jfedor2/hid-remapper/custom-boards/v6/3d-printed-case/Remapper-v6-Top-with-labels.stl

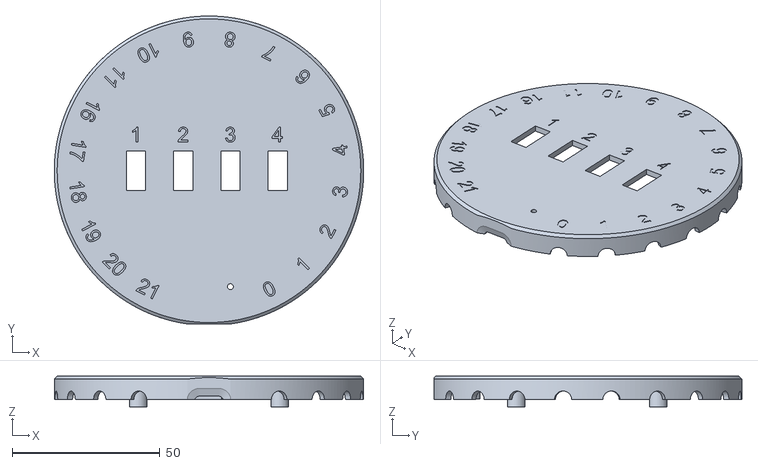
[picture p27: CAD file, 2024-04-09, an earlier design]
custom-boards/v6/3d-printed-case/Remapper-v6-Top-with-labels.stl
104.8 x 104.3 x 10.4
