jfedor2/hid-remapper/custom-boards/v7/3d-printed-case/Remapper-v7-Top-with-labels.stl

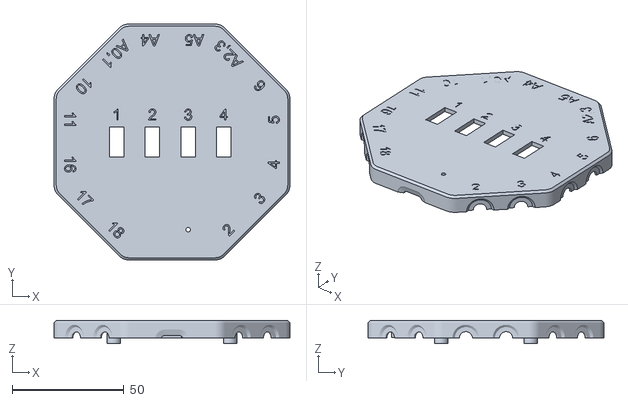
[picture p28: CAD file, 2024-04-09, an earlier design]
custom-boards/v7/3d-printed-case/Remapper-v7-Top-with-labels.stl
105.6 x 105.6 x 10.4
