jfedor2/hid-remapper/custom-boards/v1/3d-printed-case/Remapper-v1-Bottom.stl

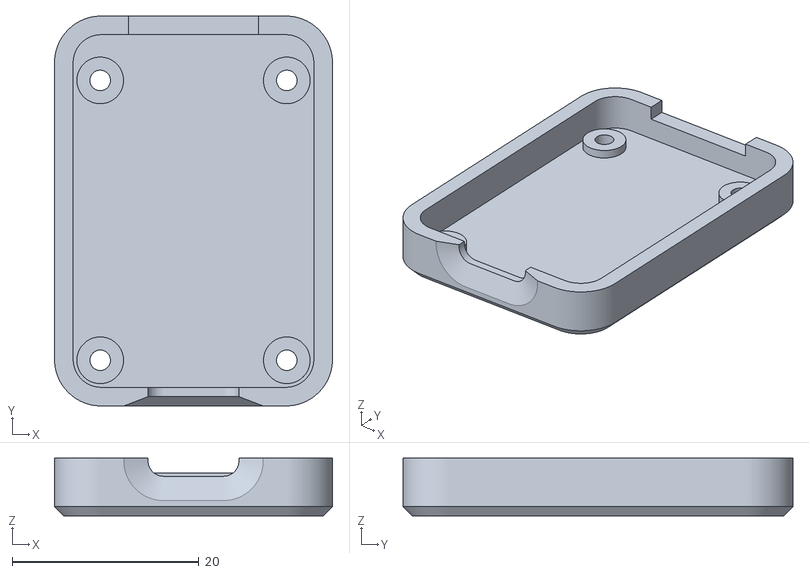
[picture p29: CAD file, 2022-11-09, an earlier design]
custom-boards/v1/3d-printed-case/Remapper-v1-Bottom.stl
29.8 x 41.8 x 6.20
