jfedor2/hid-remapper/firmware/src/boards/waveshare_rp2350_pizero.h

// -----------------------------------------------------
// NOTE: THIS HEADER IS ALSO INCLUDED BY ASSEMBLER SO
//       SHOULD ONLY CONSIST OF PREPROCESSOR DIRECTIVES
// -----------------------------------------------------

// pico_cmake_set PICO_PLATFORM=rp2350

#ifndef _BOARDS_WAVESHARE_RP2350_PIZERO_H
#define _BOARDS_WAVESHARE_RP2350_PIZERO_H

#define WAVESHARE_RP2350_PIZERO_BOARD

#define PICO_RP2350B 1

#define GPIO_VALID_PINS_BASE 0b00111111111111111111111111111111

#define PICO_DEFAULT_PIO_USB_DP_PIN 28

// --- FLASH ---

#define PICO_BOOT_STAGE2_CHOOSE_W25Q080 1

#ifndef PICO_FLASH_SPI_CLKDIV
#define PICO_FLASH_SPI_CLKDIV 2
#endif

#ifndef PICO_FLASH_SIZE_BYTES
#define PICO_FLASH_SIZE_BYTES (16 * 1024 * 1024)
#endif

#ifndef PICO_RP2350_A2_SUPPORTED
#define PICO_RP2350_A2_SUPPORTED 1
#endif

#endif
