jfedor2/hid-remapper/firmware/src/globals.cc

#include "globals.h"

std::unordered_map<uint16_t, std::unordered_map<uint8_t, std::unordered_map<uint32_t, usage_def_t>>> their_usages;
std::unordered_map<uint16_t, std::unordered_map<uint8_t, std::unordered_map<uint32_t, usage_def_t>>> their_out_usages;
std::unordered_map<uint16_t, std::unordered_map<uint8_t, std::unordered_map<uint32_t, usage_def_t>>> their_feature_usages;

std::unordered_map<uint16_t, bool> has_report_id_theirs;

std::unordered_map<uint32_t, uint8_t*> out_reports;
std::unordered_map<uint32_t, uint8_t*> prev_out_reports;
std::unordered_map<uint32_t, uint8_t> out_report_sizes;
std::unordered_map<uint32_t, std::vector<uint32_t>> their_out_usages_flat;

std::unordered_map<uint16_t, uint8_t> interface_index;
uint32_t interface_index_in_use = 0;

std::vector<usage_rle_t> our_usages_rle;
std::vector<usage_rle_t> their_usages_rle;

volatile bool need_to_persist_config = false;
volatile bool their_descriptor_updated = false;
volatile bool suspended = false;
volatile bool resume_pending = false;
volatile bool config_updated = false;

uint8_t unmapped_passthrough_layer_mask = 0b11111111;
uint32_t partial_scroll_timeout = 1000000;
uint32_t tap_hold_threshold = 200000;
uint64_t gpio_debounce_time = 5000;
uint8_t our_descriptor_number = 0;
bool ignore_auth_dev_inputs = false;
uint8_t macro_entry_duration = 0;  // 0 means 1ms
uint8_t gpio_output_mode = 0;
bool normalize_gamepad_inputs = true;

std::vector<mapping_config11_t> config_mappings;

uint8_t resolution_multiplier = 0;

std::vector<std::vector<uint32_t>> macros[NMACROS];

std::vector<expr_elem_t> expressions[NEXPRESSIONS];

bool monitor_enabled = false;

const our_descriptor_def_t* our_descriptor;

uint8_t gpio_out_state[4] = { 0 };
uint16_t digipot_state[NDIGIPOTS] = { 0 };

std::vector<quirk_t> quirks;

bool boot_protocol_keyboard = false;
bool boot_protocol_updated = false;

volatile PersistConfigReturnCode persist_config_return_code = PersistConfigReturnCode::UNKNOWN;
