jfedor2/hid-remapper/config-tool-web/usages.js

const usages = {
    'source_0': {
        "0x00090001": { 'name': 'Left button', 'class': 'mouse' },
        "0x00090002": { 'name': 'Right button', 'class': 'mouse' },
        "0x00090003": { 'name': 'Middle button', 'class': 'mouse' },
        "0x00090004": { 'name': 'Back', 'class': 'mouse' },
        "0x00090005": { 'name': 'Forward', 'class': 'mouse' },
        "0x00090006": { 'name': 'Button 6', 'class': 'mouse' },
        "0x00090007": { 'name': 'Button 7', 'class': 'mouse' },
        "0x00090008": { 'name': 'Button 8', 'class': 'mouse' },
        "0x00010030": { 'name': 'Cursor X', 'class': 'mouse' },
        "0x00010031": { 'name': 'Cursor Y', 'class': 'mouse' },
        "0x00010038": { 'name': 'V scroll', 'class': 'mouse' },
        "0x000c0238": { 'name': 'H scroll', 'class': 'mouse' },
    },
    'source_1': {
        "0x00010030": { 'name': 'Left stick X', 'class': 'gamepad' },
        "0x00010031": { 'name': 'Left stick Y', 'class': 'gamepad' },
        "0x00010032": { 'name': 'Right stick X', 'class': 'gamepad' },
        "0x00010035": { 'name': 'Right stick Y', 'class': 'gamepad' },
        "0xfff90001": { 'name': 'D-pad left', 'class': 'gamepad' },
        "0xfff90002": { 'name': 'D-pad right', 'class': 'gamepad' },
        "0xfff90003": { 'name': 'D-pad up', 'class': 'gamepad' },
        "0xfff90004": { 'name': 'D-pad down', 'class': 'gamepad' },
        "0x00090001": { 'name': 'West', 'class': 'gamepad' },
        "0x00090002": { 'name': 'South', 'class': 'gamepad' },
        "0x00090003": { 'name': 'East', 'class': 'gamepad' },
        "0x00090004": { 'name': 'North', 'class': 'gamepad' },
        "0x00090005": { 'name': 'L1', 'class': 'gamepad' },
        "0x00090006": { 'name': 'R1', 'class': 'gamepad' },
        "0x00090007": { 'name': 'L2', 'class': 'gamepad' },
        "0x00090008": { 'name': 'R2', 'class': 'gamepad' },
        "0x00010033": { 'name': 'L2 axis', 'class': 'gamepad' },
        "0x00010034": { 'name': 'R2 axis', 'class': 'gamepad' },
        "0x00090009": { 'name': 'Select', 'class': 'gamepad' },
        "0x0009000a": { 'name': 'Start', 'class': 'gamepad' },
        "0x0009000b": { 'name': 'L3', 'class': 'gamepad' },
        "0x0009000c": { 'name': 'R3', 'class': 'gamepad' },
        "0x0009000d": { 'name': 'Home', 'class': 'gamepad' },
        "0x0009000e": { 'name': 'Button 14', 'class': 'gamepad' },
        "0x0009000f": { 'name': 'Button 15', 'class': 'gamepad' },
        "0x00090010": { 'name': 'Button 16', 'class': 'gamepad' },
    },
    'source_extra': {
        "0x00010038": { 'name': 'V scroll', 'class': 'mouse' },
        "0x000c0238": { 'name': 'H scroll', 'class': 'mouse' },
        "0x00010032": { 'name': 'Right stick X', 'class': 'gamepad' },
        "0x00010035": { 'name': 'Right stick Y', 'class': 'gamepad' },
        "0xfff90001": { 'name': 'D-pad left', 'class': 'gamepad' },
        "0xfff90002": { 'name': 'D-pad right', 'class': 'gamepad' },
        "0xfff90003": { 'name': 'D-pad up', 'class': 'gamepad' },
        "0xfff90004": { 'name': 'D-pad down', 'class': 'gamepad' },
        "0x00010033": { 'name': 'L2 axis', 'class': 'gamepad' },
        "0x00010034": { 'name': 'R2 axis', 'class': 'gamepad' },
        "0x000200c5": { 'name': 'Brake', 'class': 'mouse' },
        "0x000200c4": { 'name': 'Accelerator', 'class': 'mouse' },
    },
    'source': {
        "0x000700e0": { 'name': 'Left Control', 'class': 'keyboard' },
        "0x000700e1": { 'name': 'Left Shift', 'class': 'keyboard' },
        "0x000700e2": { 'name': 'Left Alt', 'class': 'keyboard' },
        "0x000700e3": { 'name': 'Left GUI', 'class': 'keyboard' },
        "0x000700e4": { 'name': 'Right Control', 'class': 'keyboard' },
        "0x000700e5": { 'name': 'Right Shift', 'class': 'keyboard' },
        "0x000700e6": { 'name': 'Right Alt', 'class': 'keyboard' },
        "0x000700e7": { 'name': 'Right GUI', 'class': 'keyboard' },
        "0x00070004": { 'name': 'A', 'class': 'keyboard' },
        "0x00070005": { 'name': 'B', 'class': 'keyboard' },
        "0x00070006": { 'name': 'C', 'class': 'keyboard' },
        "0x00070007": { 'name': 'D', 'class': 'keyboard' },
        "0x00070008": { 'name': 'E', 'class': 'keyboard' },
        "0x00070009": { 'name': 'F', 'class': 'keyboard' },
        "0x0007000a": { 'name': 'G', 'class': 'keyboard' },
        "0x0007000b": { 'name': 'H', 'class': 'keyboard' },
        "0x0007000c": { 'name': 'I', 'class': 'keyboard' },
        "0x0007000d": { 'name': 'J', 'class': 'keyboard' },
        "0x0007000e": { 'name': 'K', 'class': 'keyboard' },
        "0x0007000f": { 'name': 'L', 'class': 'keyboard' },
        "0x00070010": { 'name': 'M', 'class': 'keyboard' },
        "0x00070011": { 'name': 'N', 'class': 'keyboard' },
        "0x00070012": { 'name': 'O', 'class': 'keyboard' },
        "0x00070013": { 'name': 'P', 'class': 'keyboard' },
        "0x00070014": { 'name': 'Q', 'class': 'keyboard' },
        "0x00070015": { 'name': 'R', 'class': 'keyboard' },
        "0x00070016": { 'name': 'S', 'class': 'keyboard' },
        "0x00070017": { 'name': 'T', 'class': 'keyboard' },
        "0x00070018": { 'name': 'U', 'class': 'keyboard' },
        "0x00070019": { 'name': 'V', 'class': 'keyboard' },
        "0x0007001a": { 'name': 'W', 'class': 'keyboard' },
        "0x0007001b": { 'name': 'X', 'class': 'keyboard' },
        "0x0007001c": { 'name': 'Y', 'class': 'keyboard' },
        "0x0007001d": { 'name': 'Z', 'class': 'keyboard' },
        "0x0007001e": { 'name': '1', 'class': 'keyboard' },
        "0x0007001f": { 'name': '2', 'class': 'keyboard' },
        "0x00070020": { 'name': '3', 'class': 'keyboard' },
        "0x00070021": { 'name': '4', 'class': 'keyboard' },
        "0x00070022": { 'name': '5', 'class': 'keyboard' },
        "0x00070023": { 'name': '6', 'class': 'keyboard' },
        "0x00070024": { 'name': '7', 'class': 'keyboard' },
        "0x00070025": { 'name': '8', 'class': 'keyboard' },
        "0x00070026": { 'name': '9', 'class': 'keyboard' },
        "0x00070027": { 'name': '0', 'class': 'keyboard' },
        "0x00070028": { 'name': 'Enter', 'class': 'keyboard' },
        "0x00070029": { 'name': 'Escape', 'class': 'keyboard' },
        "0x0007002a": { 'name': 'Backspace', 'class': 'keyboard' },
        "0x0007002b": { 'name': 'Tab', 'class': 'keyboard' },
        "0x0007002c": { 'name': 'Space', 'class': 'keyboard' },
        "0x00070039": { 'name': 'Caps Lock', 'class': 'keyboard' },
        "0x00070046": { 'name': 'PrintScreen', 'class': 'keyboard' },
        "0x00070047": { 'name': 'Scroll Lock', 'class': 'keyboard' },
        "0x00070048": { 'name': 'Pause', 'class': 'keyboard' },
        "0x00070049": { 'name': 'Insert', 'class': 'keyboard' },
        "0x0007004a": { 'name': 'Home', 'class': 'keyboard' },
        "0x0007004b": { 'name': 'PageUp', 'class': 'keyboard' },
        "0x0007004c": { 'name': 'Delete', 'class': 'keyboard' },
        "0x0007004d": { 'name': 'End', 'class': 'keyboard' },
        "0x0007004e": { 'name': 'PageDown', 'class': 'keyboard' },
        "0x0007004f": { 'name': 'Right arrow', 'class': 'keyboard' },
        "0x00070050": { 'name': 'Left arrow', 'class': 'keyboard' },
        "0x00070051": { 'name': 'Down arrow', 'class': 'keyboard' },
        "0x00070052": { 'name': 'Up arrow', 'class': 'keyboard' },
        "0x00070053": { 'name': 'Num Lock', 'class': 'keyboard' },
        "0x0007002d": { 'name': '- _', 'class': 'keyboard' },
        "0x0007002e": { 'name': '= +', 'class': 'keyboard' },
        "0x0007002f": { 'name': '[ {', 'class': 'keyboard' },
        "0x00070030": { 'name': '] }', 'class': 'keyboard' },
        "0x00070031": { 'name': '\\ |', 'class': 'keyboard' },
        "0x00070033": { 'name': '; :', 'class': 'keyboard' },
        "0x00070034": { 'name': '‘ “', 'class': 'keyboard' },
        "0x00070035": { 'name': '` ~', 'class': 'keyboard' },
        "0x00070036": { 'name': ', <', 'class': 'keyboard' },
        "0x00070037": { 'name': '. >', 'class': 'keyboard' },
        "0x00070038": { 'name': '/ ?', 'class': 'keyboard' },
        "0x0007003a": { 'name': 'F1', 'class': 'keyboard' },
        "0x0007003b": { 'name': 'F2', 'class': 'keyboard' },
        "0x0007003c": { 'name': 'F3', 'class': 'keyboard' },
        "0x0007003d": { 'name': 'F4', 'class': 'keyboard' },
        "0x0007003e": { 'name': 'F5', 'class': 'keyboard' },
        "0x0007003f": { 'name': 'F6', 'class': 'keyboard' },
        "0x00070040": { 'name': 'F7', 'class': 'keyboard' },
        "0x00070041": { 'name': 'F8', 'class': 'keyboard' },
        "0x00070042": { 'name': 'F9', 'class': 'keyboard' },
        "0x00070043": { 'name': 'F10', 'class': 'keyboard' },
        "0x00070044": { 'name': 'F11', 'class': 'keyboard' },
        "0x00070045": { 'name': 'F12', 'class': 'keyboard' },
        "0x00070068": { 'name': 'F13', 'class': 'keyboard' },
        "0x00070069": { 'name': 'F14', 'class': 'keyboard' },
        "0x0007006a": { 'name': 'F15', 'class': 'keyboard' },
        "0x0007006b": { 'name': 'F16', 'class': 'keyboard' },
        "0x0007006c": { 'name': 'F17', 'class': 'keyboard' },
        "0x0007006d": { 'name': 'F18', 'class': 'keyboard' },
        "0x0007006e": { 'name': 'F19', 'class': 'keyboard' },
        "0x0007006f": { 'name': 'F20', 'class': 'keyboard' },
        "0x00070070": { 'name': 'F21', 'class': 'keyboard' },
        "0x00070071": { 'name': 'F22', 'class': 'keyboard' },
        "0x00070072": { 'name': 'F23', 'class': 'keyboard' },
        "0x00070073": { 'name': 'F24', 'class': 'keyboard' },
        "0x00070054": { 'name': 'Keypad /', 'class': 'keyboard' },
        "0x00070055": { 'name': 'Keypad *', 'class': 'keyboard' },
        "0x00070056": { 'name': 'Keypad -', 'class': 'keyboard' },
        "0x00070057": { 'name': 'Keypad +', 'class': 'keyboard' },
        "0x00070058": { 'name': 'Keypad Enter', 'class': 'keyboard' },
        "0x00070059": { 'name': 'Keypad 1', 'class': 'keyboard' },
        "0x0007005a": { 'name': 'Keypad 2', 'class': 'keyboard' },
        "0x0007005b": { 'name': 'Keypad 3', 'class': 'keyboard' },
        "0x0007005c": { 'name': 'Keypad 4', 'class': 'keyboard' },
        "0x0007005d": { 'name': 'Keypad 5', 'class': 'keyboard' },
        "0x0007005e": { 'name': 'Keypad 6', 'class': 'keyboard' },
        "0x0007005f": { 'name': 'Keypad 7', 'class': 'keyboard' },
        "0x00070060": { 'name': 'Keypad 8', 'class': 'keyboard' },
        "0x00070061": { 'name': 'Keypad 9', 'class': 'keyboard' },
        "0x00070062": { 'name': 'Keypad 0', 'class': 'keyboard' },
        "0x00070063": { 'name': 'Keypad .', 'class': 'keyboard' },
        "0x00070067": { 'name': 'Keypad =', 'class': 'keyboard' },
        "0x00070064": { 'name': 'Non-US \\ |', 'class': 'keyboard' },
        "0x00070032": { 'name': 'Non-US # ~', 'class': 'keyboard' },
        "0x00070065": { 'name': 'Application', 'class': 'keyboard' },
        "0x00070066": { 'name': 'Power', 'class': 'keyboard' },
        "0x00070087": { 'name': '\\ _', 'class': 'keyboard' },
        "0x00070089": { 'name': '¥ |', 'class': 'keyboard' },
        "0x0007008a": { 'name': 'Henkan', 'class': 'keyboard' },
        "0x0007008b": { 'name': 'Muhenkan', 'class': 'keyboard' },
        "0x00070088": { 'name': 'Kana', 'class': 'keyboard' },
        "0x00070090": { 'name': 'Kana (Mac)', 'class': 'keyboard' },
        "0x00070091": { 'name': 'Eisū (Mac)', 'class': 'keyboard' },
        "0x00080001": { 'name': 'Num Lock LED', 'class': 'keyboard' },
        "0x00080002": { 'name': 'Caps Lock LED', 'class': 'keyboard' },
        "0x00080003": { 'name': 'Scroll Lock LED', 'class': 'keyboard' },
        "0x00080004": { 'name': 'Compose LED', 'class': 'keyboard' },
        "0x00080005": { 'name': 'Kana LED', 'class': 'keyboard' },

        "0x000c00e9": { 'name': 'Volume up', 'class': 'media' },
        "0x000c00ea": { 'name': 'Volume down', 'class': 'media' },
        "0x000c00e2": { 'name': 'Mute', 'class': 'media' },
        "0x000b002f": { 'name': 'Mic mute', 'class': 'media' },
        "0x000c00cd": { 'name': 'Play/pause', 'class': 'media' },
        "0x000c00b7": { 'name': 'Stop', 'class': 'media' },
        "0x000c00b5": { 'name': 'Next track', 'class': 'media' },
        "0x000c00b6": { 'name': 'Previous track', 'class': 'media' },

        "0x00000000": { 'name': 'Nothing', 'class': 'other' },
        "0xfff30001": { 'name': 'Expression 1', 'class': 'other' },
        "0xfff30002": { 'name': 'Expression 2', 'class': 'other' },
        "0xfff30003": { 'name': 'Expression 3', 'class': 'other' },
        "0xfff30004": { 'name': 'Expression 4', 'class': 'other' },
        "0xfff30005": { 'name': 'Expression 5', 'class': 'other' },
        "0xfff30006": { 'name': 'Expression 6', 'class': 'other' },
        "0xfff30007": { 'name': 'Expression 7', 'class': 'other' },
        "0xfff30008": { 'name': 'Expression 8', 'class': 'other' },
        "0xfff50001": { 'name': 'Register 1', 'class': 'other' },
        "0xfff50002": { 'name': 'Register 2', 'class': 'other' },
        "0xfff50003": { 'name': 'Register 3', 'class': 'other' },
        "0xfff50004": { 'name': 'Register 4', 'class': 'other' },
        "0xfff50005": { 'name': 'Register 5', 'class': 'other' },
        "0xfff50006": { 'name': 'Register 6', 'class': 'other' },
        "0xfff50007": { 'name': 'Register 7', 'class': 'other' },
        "0xfff50008": { 'name': 'Register 8', 'class': 'other' },
        "0xfff50009": { 'name': 'Register 9', 'class': 'other' },
        "0xfff5000a": { 'name': 'Register 10', 'class': 'other' },
        "0xfff5000b": { 'name': 'Register 11', 'class': 'other' },
        "0xfff5000c": { 'name': 'Register 12', 'class': 'other' },
        "0xfff5000d": { 'name': 'Register 13', 'class': 'other' },
        "0xfff5000e": { 'name': 'Register 14', 'class': 'other' },
        "0xfff5000f": { 'name': 'Register 15', 'class': 'other' },
        "0xfff50010": { 'name': 'Register 16', 'class': 'other' },
        "0xfff50011": { 'name': 'Register 17', 'class': 'other' },
        "0xfff50012": { 'name': 'Register 18', 'class': 'other' },
        "0xfff50013": { 'name': 'Register 19', 'class': 'other' },
        "0xfff50014": { 'name': 'Register 20', 'class': 'other' },
        "0xfff50015": { 'name': 'Register 21', 'class': 'other' },
        "0xfff50016": { 'name': 'Register 22', 'class': 'other' },
        "0xfff50017": { 'name': 'Register 23', 'class': 'other' },
        "0xfff50018": { 'name': 'Register 24', 'class': 'other' },
        "0xfff50019": { 'name': 'Register 25', 'class': 'other' },
        "0xfff5001a": { 'name': 'Register 26', 'class': 'other' },
        "0xfff5001b": { 'name': 'Register 27', 'class': 'other' },
        "0xfff5001c": { 'name': 'Register 28', 'class': 'other' },
        "0xfff5001d": { 'name': 'Register 29', 'class': 'other' },
        "0xfff5001e": { 'name': 'Register 30', 'class': 'other' },
        "0xfff5001f": { 'name': 'Register 31', 'class': 'other' },
        "0xfff50020": { 'name': 'Register 32', 'class': 'other' },
        "0xfff40000": { 'name': 'GPIO 0', 'class': 'other' },
        "0xfff40001": { 'name': 'GPIO 1', 'class': 'other' },
        "0xfff40002": { 'name': 'GPIO 2', 'class': 'other' },
        "0xfff40003": { 'name': 'GPIO 3', 'class': 'other' },
        "0xfff40004": { 'name': 'GPIO 4', 'class': 'other' },
        "0xfff40005": { 'name': 'GPIO 5', 'class': 'other' },
        "0xfff40006": { 'name': 'GPIO 6', 'class': 'other' },
        "0xfff40007": { 'name': 'GPIO 7', 'class': 'other' },
        "0xfff40008": { 'name': 'GPIO 8', 'class': 'other' },
        "0xfff40009": { 'name': 'GPIO 9', 'class': 'other' },
        "0xfff4000a": { 'name': 'GPIO 10', 'class': 'other' },
        "0xfff4000b": { 'name': 'GPIO 11', 'class': 'other' },
        "0xfff4000c": { 'name': 'GPIO 12', 'class': 'other' },
        "0xfff4000d": { 'name': 'GPIO 13', 'class': 'other' },
        "0xfff4000e": { 'name': 'GPIO 14', 'class': 'other' },
        "0xfff4000f": { 'name': 'GPIO 15', 'class': 'other' },
        "0xfff40010": { 'name': 'GPIO 16', 'class': 'other' },
        "0xfff40011": { 'name': 'GPIO 17', 'class': 'other' },
        "0xfff40012": { 'name': 'GPIO 18', 'class': 'other' },
        "0xfff40013": { 'name': 'GPIO 19', 'class': 'other' },
        "0xfff40014": { 'name': 'GPIO 20', 'class': 'other' },
        "0xfff40015": { 'name': 'GPIO 21', 'class': 'other' },
        "0xfff40016": { 'name': 'GPIO 22', 'class': 'other' },
        "0xfff40017": { 'name': 'GPIO 23', 'class': 'other' },
        "0xfff40018": { 'name': 'GPIO 24', 'class': 'other' },
        "0xfff40019": { 'name': 'GPIO 25', 'class': 'other' },
        "0xfff4001a": { 'name': 'GPIO 26', 'class': 'other' },
        "0xfff4001b": { 'name': 'GPIO 27', 'class': 'other' },
        "0xfff4001c": { 'name': 'GPIO 28', 'class': 'other' },
        "0xfff4001d": { 'name': 'GPIO 29', 'class': 'other' },
    },
    0: {
        "0x00090001": { 'name': 'Left button', 'class': 'mouse' },
        "0x00090002": { 'name': 'Right button', 'class': 'mouse' },
        "0x00090003": { 'name': 'Middle button', 'class': 'mouse' },
        "0x00090004": { 'name': 'Back', 'class': 'mouse' },
        "0x00090005": { 'name': 'Forward', 'class': 'mouse' },
        "0x00090006": { 'name': 'Button 6', 'class': 'mouse' },
        "0x00090007": { 'name': 'Button 7', 'class': 'mouse' },
        "0x00090008": { 'name': 'Button 8', 'class': 'mouse' },
        "0x00010030": { 'name': 'Cursor X', 'class': 'mouse' },
        "0x00010031": { 'name': 'Cursor Y', 'class': 'mouse' },
        "0x00010038": { 'name': 'V scroll', 'class': 'mouse' },
        "0x000c0238": { 'name': 'H scroll', 'class': 'mouse' },

        "0x000700e0": { 'name': 'Left Control', 'class': 'keyboard' },
        "0x000700e1": { 'name': 'Left Shift', 'class': 'keyboard' },
        "0x000700e2": { 'name': 'Left Alt', 'class': 'keyboard' },
        "0x000700e3": { 'name': 'Left GUI', 'class': 'keyboard' },
        "0x000700e4": { 'name': 'Right Control', 'class': 'keyboard' },
        "0x000700e5": { 'name': 'Right Shift', 'class': 'keyboard' },
        "0x000700e6": { 'name': 'Right Alt', 'class': 'keyboard' },
        "0x000700e7": { 'name': 'Right GUI', 'class': 'keyboard' },
        "0x00070004": { 'name': 'A', 'class': 'keyboard' },
        "0x00070005": { 'name': 'B', 'class': 'keyboard' },
        "0x00070006": { 'name': 'C', 'class': 'keyboard' },
        "0x00070007": { 'name': 'D', 'class': 'keyboard' },
        "0x00070008": { 'name': 'E', 'class': 'keyboard' },
        "0x00070009": { 'name': 'F', 'class': 'keyboard' },
        "0x0007000a": { 'name': 'G', 'class': 'keyboard' },
        "0x0007000b": { 'name': 'H', 'class': 'keyboard' },
        "0x0007000c": { 'name': 'I', 'class': 'keyboard' },
        "0x0007000d": { 'name': 'J', 'class': 'keyboard' },
        "0x0007000e": { 'name': 'K', 'class': 'keyboard' },
        "0x0007000f": { 'name': 'L', 'class': 'keyboard' },
        "0x00070010": { 'name': 'M', 'class': 'keyboard' },
        "0x00070011": { 'name': 'N', 'class': 'keyboard' },
        "0x00070012": { 'name': 'O', 'class': 'keyboard' },
        "0x00070013": { 'name': 'P', 'class': 'keyboard' },
        "0x00070014": { 'name': 'Q', 'class': 'keyboard' },
        "0x00070015": { 'name': 'R', 'class': 'keyboard' },
        "0x00070016": { 'name': 'S', 'class': 'keyboard' },
        "0x00070017": { 'name': 'T', 'class': 'keyboard' },
        "0x00070018": { 'name': 'U', 'class': 'keyboard' },
        "0x00070019": { 'name': 'V', 'class': 'keyboard' },
        "0x0007001a": { 'name': 'W', 'class': 'keyboard' },
        "0x0007001b": { 'name': 'X', 'class': 'keyboard' },
        "0x0007001c": { 'name': 'Y', 'class': 'keyboard' },
        "0x0007001d": { 'name': 'Z', 'class': 'keyboard' },
        "0x0007001e": { 'name': '1', 'class': 'keyboard' },
        "0x0007001f": { 'name': '2', 'class': 'keyboard' },
        "0x00070020": { 'name': '3', 'class': 'keyboard' },
        "0x00070021": { 'name': '4', 'class': 'keyboard' },
        "0x00070022": { 'name': '5', 'class': 'keyboard' },
        "0x00070023": { 'name': '6', 'class': 'keyboard' },
        "0x00070024": { 'name': '7', 'class': 'keyboard' },
        "0x00070025": { 'name': '8', 'class': 'keyboard' },
        "0x00070026": { 'name': '9', 'class': 'keyboard' },
        "0x00070027": { 'name': '0', 'class': 'keyboard' },
        "0x00070028": { 'name': 'Enter', 'class': 'keyboard' },
        "0x00070029": { 'name': 'Escape', 'class': 'keyboard' },
        "0x0007002a": { 'name': 'Backspace', 'class': 'keyboard' },
        "0x0007002b": { 'name': 'Tab', 'class': 'keyboard' },
        "0x0007002c": { 'name': 'Space', 'class': 'keyboard' },
        "0x00070039": { 'name': 'Caps Lock', 'class': 'keyboard' },
        "0x00070046": { 'name': 'PrintScreen', 'class': 'keyboard' },
        "0x00070047": { 'name': 'Scroll Lock', 'class': 'keyboard' },
        "0x00070048": { 'name': 'Pause', 'class': 'keyboard' },
        "0x00070049": { 'name': 'Insert', 'class': 'keyboard' },
        "0x0007004a": { 'name': 'Home', 'class': 'keyboard' },
        "0x0007004b": { 'name': 'PageUp', 'class': 'keyboard' },
        "0x0007004c": { 'name': 'Delete', 'class': 'keyboard' },
        "0x0007004d": { 'name': 'End', 'class': 'keyboard' },
        "0x0007004e": { 'name': 'PageDown', 'class': 'keyboard' },
        "0x0007004f": { 'name': 'Right arrow', 'class': 'keyboard' },
        "0x00070050": { 'name': 'Left arrow', 'class': 'keyboard' },
        "0x00070051": { 'name': 'Down arrow', 'class': 'keyboard' },
        "0x00070052": { 'name': 'Up arrow', 'class': 'keyboard' },
        "0x00070053": { 'name': 'Num Lock', 'class': 'keyboard' },
        "0x0007002d": { 'name': '- _', 'class': 'keyboard' },
        "0x0007002e": { 'name': '= +', 'class': 'keyboard' },
        "0x0007002f": { 'name': '[ {', 'class': 'keyboard' },
        "0x00070030": { 'name': '] }', 'class': 'keyboard' },
        "0x00070031": { 'name': '\\ |', 'class': 'keyboard' },
        "0x00070033": { 'name': '; :', 'class': 'keyboard' },
        "0x00070034": { 'name': '‘ “', 'class': 'keyboard' },
        "0x00070035": { 'name': '` ~', 'class': 'keyboard' },
        "0x00070036": { 'name': ', <', 'class': 'keyboard' },
        "0x00070037": { 'name': '. >', 'class': 'keyboard' },
        "0x00070038": { 'name': '/ ?', 'class': 'keyboard' },
        "0x0007003a": { 'name': 'F1', 'class': 'keyboard' },
        "0x0007003b": { 'name': 'F2', 'class': 'keyboard' },
        "0x0007003c": { 'name': 'F3', 'class': 'keyboard' },
        "0x0007003d": { 'name': 'F4', 'class': 'keyboard' },
        "0x0007003e": { 'name': 'F5', 'class': 'keyboard' },
        "0x0007003f": { 'name': 'F6', 'class': 'keyboard' },
        "0x00070040": { 'name': 'F7', 'class': 'keyboard' },
        "0x00070041": { 'name': 'F8', 'class': 'keyboard' },
        "0x00070042": { 'name': 'F9', 'class': 'keyboard' },
        "0x00070043": { 'name': 'F10', 'class': 'keyboard' },
        "0x00070044": { 'name': 'F11', 'class': 'keyboard' },
        "0x00070045": { 'name': 'F12', 'class': 'keyboard' },
        "0x00070068": { 'name': 'F13', 'class': 'keyboard' },
        "0x00070069": { 'name': 'F14', 'class': 'keyboard' },
        "0x0007006a": { 'name': 'F15', 'class': 'keyboard' },
        "0x0007006b": { 'name': 'F16', 'class': 'keyboard' },
        "0x0007006c": { 'name': 'F17', 'class': 'keyboard' },
        "0x0007006d": { 'name': 'F18', 'class': 'keyboard' },
        "0x0007006e": { 'name': 'F19', 'class': 'keyboard' },
        "0x0007006f": { 'name': 'F20', 'class': 'keyboard' },
        "0x00070070": { 'name': 'F21', 'class': 'keyboard' },
        "0x00070071": { 'name': 'F22', 'class': 'keyboard' },
        "0x00070072": { 'name': 'F23', 'class': 'keyboard' },
        "0x00070073": { 'name': 'F24', 'class': 'keyboard' },
        "0x00070054": { 'name': 'Keypad /', 'class': 'keyboard' },
        "0x00070055": { 'name': 'Keypad *', 'class': 'keyboard' },
        "0x00070056": { 'name': 'Keypad -', 'class': 'keyboard' },
        "0x00070057": { 'name': 'Keypad +', 'class': 'keyboard' },
        "0x00070058": { 'name': 'Keypad Enter', 'class': 'keyboard' },
        "0x00070059": { 'name': 'Keypad 1', 'class': 'keyboard' },
        "0x0007005a": { 'name': 'Keypad 2', 'class': 'keyboard' },
        "0x0007005b": { 'name': 'Keypad 3', 'class': 'keyboard' },
        "0x0007005c": { 'name': 'Keypad 4', 'class': 'keyboard' },
        "0x0007005d": { 'name': 'Keypad 5', 'class': 'keyboard' },
        "0x0007005e": { 'name': 'Keypad 6', 'class': 'keyboard' },
        "0x0007005f": { 'name': 'Keypad 7', 'class': 'keyboard' },
        "0x00070060": { 'name': 'Keypad 8', 'class': 'keyboard' },
        "0x00070061": { 'name': 'Keypad 9', 'class': 'keyboard' },
        "0x00070062": { 'name': 'Keypad 0', 'class': 'keyboard' },
        "0x00070063": { 'name': 'Keypad .', 'class': 'keyboard' },
        "0x00070067": { 'name': 'Keypad =', 'class': 'keyboard' },
        "0x00070064": { 'name': 'Non-US \\ |', 'class': 'keyboard' },
        "0x00070032": { 'name': 'Non-US # ~', 'class': 'keyboard' },
        "0x00070065": { 'name': 'Application', 'class': 'keyboard' },
        "0x00070066": { 'name': 'Power', 'class': 'keyboard' },
        "0x00070087": { 'name': '\\ _', 'class': 'keyboard' },
        "0x00070089": { 'name': '¥ |', 'class': 'keyboard' },
        "0x0007008a": { 'name': 'Henkan', 'class': 'keyboard' },
        "0x0007008b": { 'name': 'Muhenkan', 'class': 'keyboard' },
        "0x00070088": { 'name': 'Kana', 'class': 'keyboard' },
        "0x00070090": { 'name': 'Kana (Mac)', 'class': 'keyboard' },
        "0x00070091": { 'name': 'Eisū (Mac)', 'class': 'keyboard' },
        "0x00080001": { 'name': 'Num Lock LED', 'class': 'keyboard' },
        "0x00080002": { 'name': 'Caps Lock LED', 'class': 'keyboard' },
        "0x00080003": { 'name': 'Scroll Lock LED', 'class': 'keyboard' },
        "0x00080004": { 'name': 'Compose LED', 'class': 'keyboard' },
        "0x00080005": { 'name': 'Kana LED', 'class': 'keyboard' },

        "0x000c00e9": { 'name': 'Volume up', 'class': 'media' },
        "0x000c00ea": { 'name': 'Volume down', 'class': 'media' },
        "0x000c00e2": { 'name': 'Mute', 'class': 'media' },
        "0x000b002f": { 'name': 'Mic mute', 'class': 'media' },
        "0x000c00cd": { 'name': 'Play/pause', 'class': 'media' },
        "0x000c00b7": { 'name': 'Stop', 'class': 'media' },
        "0x000c00b5": { 'name': 'Next track', 'class': 'media' },
        "0x000c00b6": { 'name': 'Previous track', 'class': 'media' },
    },
    2: {
        "0x00090001": { 'name': 'Y', 'class': 'mouse' },
        "0x00090002": { 'name': 'B', 'class': 'mouse' },
        "0x00090003": { 'name': 'A', 'class': 'mouse' },
        "0x00090004": { 'name': 'X', 'class': 'mouse' },
        "0x00090005": { 'name': 'L', 'class': 'mouse' },
        "0x00090006": { 'name': 'R', 'class': 'mouse' },
        "0x00090007": { 'name': 'ZL', 'class': 'mouse' },
        "0x00090008": { 'name': 'ZR', 'class': 'mouse' },
        "0x00090009": { 'name': 'Minus', 'class': 'mouse' },
        "0x0009000a": { 'name': 'Plus', 'class': 'mouse' },
        "0x0009000b": { 'name': 'LS', 'class': 'mouse' },
        "0x0009000c": { 'name': 'RS', 'class': 'mouse' },
        "0x0009000d": { 'name': 'Home', 'class': 'mouse' },
        "0x0009000e": { 'name': 'Capture', 'class': 'mouse' },
        "0x0009000f": { 'name': 'Button 15', 'class': 'mouse' },
        "0x00090010": { 'name': 'Button 16', 'class': 'mouse' },
        "0xfff90001": { 'name': 'D-pad left', 'class': 'mouse' },
        "0xfff90002": { 'name': 'D-pad right', 'class': 'mouse' },
        "0xfff90003": { 'name': 'D-pad up', 'class': 'mouse' },
        "0xfff90004": { 'name': 'D-pad down', 'class': 'mouse' },
        "0x00010030": { 'name': 'Left stick X', 'class': 'mouse' },
        "0x00010031": { 'name': 'Left stick Y', 'class': 'mouse' },
        "0x00010032": { 'name': 'Right stick X', 'class': 'mouse' },
        "0x00010035": { 'name': 'Right stick Y', 'class': 'mouse' },
    },
    3: {
        "0x00090001": { 'name': 'Square', 'class': 'mouse' },
        "0x00090002": { 'name': 'Cross', 'class': 'mouse' },
        "0x00090003": { 'name': 'Circle', 'class': 'mouse' },
        "0x00090004": { 'name': 'Triangle', 'class': 'mouse' },
        "0x00090005": { 'name': 'L1', 'class': 'mouse' },
        "0x00090006": { 'name': 'R1', 'class': 'mouse' },
        "0x00090007": { 'name': 'L2', 'class': 'mouse' },
        "0x00090008": { 'name': 'R2', 'class': 'mouse' },
        "0x00090009": { 'name': 'Share', 'class': 'mouse' },
        "0x0009000a": { 'name': 'Options', 'class': 'mouse' },
        "0x0009000b": { 'name': 'L3', 'class': 'mouse' },
        "0x0009000c": { 'name': 'R3', 'class': 'mouse' },
        "0x0009000d": { 'name': 'PS', 'class': 'mouse' },
        "0x0009000e": { 'name': 'Touchpad', 'class': 'mouse' },
        "0xfff90001": { 'name': 'D-pad left', 'class': 'mouse' },
        "0xfff90002": { 'name': 'D-pad right', 'class': 'mouse' },
        "0xfff90003": { 'name': 'D-pad up', 'class': 'mouse' },
        "0xfff90004": { 'name': 'D-pad down', 'class': 'mouse' },
        "0x00010030": { 'name': 'Left stick X', 'class': 'mouse' },
        "0x00010031": { 'name': 'Left stick Y', 'class': 'mouse' },
        "0x00010032": { 'name': 'Right stick X', 'class': 'mouse' },
        "0x00010035": { 'name': 'Right stick Y', 'class': 'mouse' },
        "0x00010033": { 'name': 'L2 axis', 'class': 'mouse' },
        "0x00010034": { 'name': 'R2 axis', 'class': 'mouse' },
    },
    4: {
        "0x00010030": { 'name': 'Left stick X', 'class': 'mouse' },
        "0x00010031": { 'name': 'Left stick Y', 'class': 'mouse' },
        "0x00010032": { 'name': 'Right stick X', 'class': 'mouse' },
        "0x00010035": { 'name': 'Right stick Y', 'class': 'mouse' },
        "0xfff90001": { 'name': 'D-pad left', 'class': 'mouse' },
        "0xfff90002": { 'name': 'D-pad right', 'class': 'mouse' },
        "0xfff90003": { 'name': 'D-pad up', 'class': 'mouse' },
        "0xfff90004": { 'name': 'D-pad down', 'class': 'mouse' },
        "0x00090001": { 'name': 'A', 'class': 'mouse' },
        "0x00090002": { 'name': 'B', 'class': 'mouse' },
        "0x00090004": { 'name': 'X', 'class': 'mouse' },
        "0x00090005": { 'name': 'Y', 'class': 'mouse' },
        "0x00090007": { 'name': 'L1', 'class': 'mouse' },
        "0x00090008": { 'name': 'R1', 'class': 'mouse' },
        "0x00090014": { 'name': 'L2', 'class': 'mouse' },
        "0x000200c5": { 'name': 'L2 axis', 'class': 'mouse' },
        "0x00090013": { 'name': 'R2', 'class': 'mouse' },
        "0x000200c4": { 'name': 'R2 axis', 'class': 'mouse' },
        "0x0009000e": { 'name': 'L3', 'class': 'mouse' },
        "0x0009000f": { 'name': 'R3', 'class': 'mouse' },
        "0x0009000b": { 'name': 'Options', 'class': 'mouse' },
        "0x0009000c": { 'name': 'Menu', 'class': 'mouse' },
        "0x0009000d": { 'name': 'Stadia', 'class': 'mouse' },
        "0x00090011": { 'name': 'Assistant', 'class': 'mouse' },
        "0x00090012": { 'name': 'Capture', 'class': 'mouse' },
    },
    5: {
        "0x00010030": { 'name': 'Left stick X', 'class': 'mouse' },
        "0x00010031": { 'name': 'Left stick Y', 'class': 'mouse' },
        "0x00010032": { 'name': 'Right stick X', 'class': 'mouse' },
        "0x00010035": { 'name': 'Right stick Y', 'class': 'mouse' },
        "0xfff90001": { 'name': 'D-pad left', 'class': 'mouse' },
        "0xfff90002": { 'name': 'D-pad right', 'class': 'mouse' },
        "0xfff90003": { 'name': 'D-pad up', 'class': 'mouse' },
        "0xfff90004": { 'name': 'D-pad down', 'class': 'mouse' },
        "0x00090005": { 'name': 'A', 'class': 'mouse' },
        "0x00090006": { 'name': 'B', 'class': 'mouse' },
        "0x0009000b": { 'name': 'X', 'class': 'mouse' },
        "0x0009000c": { 'name': 'Y', 'class': 'mouse' },
        "0x00090004": { 'name': 'LB', 'class': 'mouse' },
        "0x0009000a": { 'name': 'RB', 'class': 'mouse' },
        "0x00090001": { 'name': 'X1', 'class': 'mouse' },
        "0x00090002": { 'name': 'X2', 'class': 'mouse' },
        "0x00090003": { 'name': 'LSB', 'class': 'mouse' },
        "0x00090009": { 'name': 'RSB', 'class': 'mouse' },
        "0x00090007": { 'name': 'View', 'class': 'mouse' },
        "0x00090008": { 'name': 'Menu', 'class': 'mouse' },
    },
};

const common_target_usages = {
    "0x00000000": { 'name': 'Nothing', 'class': 'other' },
    "0xfff10001": { 'name': 'Layer 1', 'class': 'other' },
    "0xfff10002": { 'name': 'Layer 2', 'class': 'other' },
    "0xfff10003": { 'name': 'Layer 3', 'class': 'other' },
    "0xfff10004": { 'name': 'Layer 4', 'class': 'other' },
    "0xfff10005": { 'name': 'Layer 5', 'class': 'other' },
    "0xfff10006": { 'name': 'Layer 6', 'class': 'other' },
    "0xfff10007": { 'name': 'Layer 7', 'class': 'other' },
    "0xfff20001": { 'name': 'Macro 1', 'class': 'other' },
    "0xfff20002": { 'name': 'Macro 2', 'class': 'other' },
    "0xfff20003": { 'name': 'Macro 3', 'class': 'other' },
    "0xfff20004": { 'name': 'Macro 4', 'class': 'other' },
    "0xfff20005": { 'name': 'Macro 5', 'class': 'other' },
    "0xfff20006": { 'name': 'Macro 6', 'class': 'other' },
    "0xfff20007": { 'name': 'Macro 7', 'class': 'other' },
    "0xfff20008": { 'name': 'Macro 8', 'class': 'other' },
    "0xfff20009": { 'name': 'Macro 9', 'class': 'other' },
    "0xfff2000a": { 'name': 'Macro 10', 'class': 'other' },
    "0xfff2000b": { 'name': 'Macro 11', 'class': 'other' },
    "0xfff2000c": { 'name': 'Macro 12', 'class': 'other' },
    "0xfff2000d": { 'name': 'Macro 13', 'class': 'other' },
    "0xfff2000e": { 'name': 'Macro 14', 'class': 'other' },
    "0xfff2000f": { 'name': 'Macro 15', 'class': 'other' },
    "0xfff20010": { 'name': 'Macro 16', 'class': 'other' },
    "0xfff20011": { 'name': 'Macro 17', 'class': 'other' },
    "0xfff20012": { 'name': 'Macro 18', 'class': 'other' },
    "0xfff20013": { 'name': 'Macro 19', 'class': 'other' },
    "0xfff20014": { 'name': 'Macro 20', 'class': 'other' },
    "0xfff20015": { 'name': 'Macro 21', 'class': 'other' },
    "0xfff20016": { 'name': 'Macro 22', 'class': 'other' },
    "0xfff20017": { 'name': 'Macro 23', 'class': 'other' },
    "0xfff20018": { 'name': 'Macro 24', 'class': 'other' },
    "0xfff20019": { 'name': 'Macro 25', 'class': 'other' },
    "0xfff2001a": { 'name': 'Macro 26', 'class': 'other' },
    "0xfff2001b": { 'name': 'Macro 27', 'class': 'other' },
    "0xfff2001c": { 'name': 'Macro 28', 'class': 'other' },
    "0xfff2001d": { 'name': 'Macro 29', 'class': 'other' },
    "0xfff2001e": { 'name': 'Macro 30', 'class': 'other' },
    "0xfff2001f": { 'name': 'Macro 31', 'class': 'other' },
    "0xfff20020": { 'name': 'Macro 32', 'class': 'other' },
    "0xfff40000": { 'name': 'GPIO 0', 'class': 'other' },
    "0xfff40001": { 'name': 'GPIO 1', 'class': 'other' },
    "0xfff40002": { 'name': 'GPIO 2', 'class': 'other' },
    "0xfff40003": { 'name': 'GPIO 3', 'class': 'other' },
    "0xfff40004": { 'name': 'GPIO 4', 'class': 'other' },
    "0xfff40005": { 'name': 'GPIO 5', 'class': 'other' },
    "0xfff40006": { 'name': 'GPIO 6', 'class': 'other' },
    "0xfff40007": { 'name': 'GPIO 7', 'class': 'other' },
    "0xfff40008": { 'name': 'GPIO 8', 'class': 'other' },
    "0xfff40009": { 'name': 'GPIO 9', 'class': 'other' },
    "0xfff4000a": { 'name': 'GPIO 10', 'class': 'other' },
    "0xfff4000b": { 'name': 'GPIO 11', 'class': 'other' },
    "0xfff4000c": { 'name': 'GPIO 12', 'class': 'other' },
    "0xfff4000d": { 'name': 'GPIO 13', 'class': 'other' },
    "0xfff4000e": { 'name': 'GPIO 14', 'class': 'other' },
    "0xfff4000f": { 'name': 'GPIO 15', 'class': 'other' },
    "0xfff40010": { 'name': 'GPIO 16', 'class': 'other' },
    "0xfff40011": { 'name': 'GPIO 17', 'class': 'other' },
    "0xfff40012": { 'name': 'GPIO 18', 'class': 'other' },
    "0xfff40013": { 'name': 'GPIO 19', 'class': 'other' },
    "0xfff40014": { 'name': 'GPIO 20', 'class': 'other' },
    "0xfff40015": { 'name': 'GPIO 21', 'class': 'other' },
    "0xfff40016": { 'name': 'GPIO 22', 'class': 'other' },
    "0xfff40017": { 'name': 'GPIO 23', 'class': 'other' },
    "0xfff40018": { 'name': 'GPIO 24', 'class': 'other' },
    "0xfff40019": { 'name': 'GPIO 25', 'class': 'other' },
    "0xfff4001a": { 'name': 'GPIO 26', 'class': 'other' },
    "0xfff4001b": { 'name': 'GPIO 27', 'class': 'other' },
    "0xfff4001c": { 'name': 'GPIO 28', 'class': 'other' },
    "0xfff4001d": { 'name': 'GPIO 29', 'class': 'other' },
    "0xfff50001": { 'name': 'Register 1', 'class': 'other' },
    "0xfff50002": { 'name': 'Register 2', 'class': 'other' },
    "0xfff50003": { 'name': 'Register 3', 'class': 'other' },
    "0xfff50004": { 'name': 'Register 4', 'class': 'other' },
    "0xfff50005": { 'name': 'Register 5', 'class': 'other' },
    "0xfff50006": { 'name': 'Register 6', 'class': 'other' },
    "0xfff50007": { 'name': 'Register 7', 'class': 'other' },
    "0xfff50008": { 'name': 'Register 8', 'class': 'other' },
    "0xfff50009": { 'name': 'Register 9', 'class': 'other' },
    "0xfff5000a": { 'name': 'Register 10', 'class': 'other' },
    "0xfff5000b": { 'name': 'Register 11', 'class': 'other' },
    "0xfff5000c": { 'name': 'Register 12', 'class': 'other' },
    "0xfff5000d": { 'name': 'Register 13', 'class': 'other' },
    "0xfff5000e": { 'name': 'Register 14', 'class': 'other' },
    "0xfff5000f": { 'name': 'Register 15', 'class': 'other' },
    "0xfff50010": { 'name': 'Register 16', 'class': 'other' },
    "0xfff50011": { 'name': 'Register 17', 'class': 'other' },
    "0xfff50012": { 'name': 'Register 18', 'class': 'other' },
    "0xfff50013": { 'name': 'Register 19', 'class': 'other' },
    "0xfff50014": { 'name': 'Register 20', 'class': 'other' },
    "0xfff50015": { 'name': 'Register 21', 'class': 'other' },
    "0xfff50016": { 'name': 'Register 22', 'class': 'other' },
    "0xfff50017": { 'name': 'Register 23', 'class': 'other' },
    "0xfff50018": { 'name': 'Register 24', 'class': 'other' },
    "0xfff50019": { 'name': 'Register 25', 'class': 'other' },
    "0xfff5001a": { 'name': 'Register 26', 'class': 'other' },
    "0xfff5001b": { 'name': 'Register 27', 'class': 'other' },
    "0xfff5001c": { 'name': 'Register 28', 'class': 'other' },
    "0xfff5001d": { 'name': 'Register 29', 'class': 'other' },
    "0xfff5001e": { 'name': 'Register 30', 'class': 'other' },
    "0xfff5001f": { 'name': 'Register 31', 'class': 'other' },
    "0xfff50020": { 'name': 'Register 32', 'class': 'other' },
    "0xfff60000": { 'name': 'Analog 0', 'class': 'other' },
    "0xfff60001": { 'name': 'Analog 1', 'class': 'other' },
    "0xfff60002": { 'name': 'Analog 2', 'class': 'other' },
    "0xfff60003": { 'name': 'Analog 3', 'class': 'other' },
    "0xfff60004": { 'name': 'Analog 4', 'class': 'other' },
    "0xfff60005": { 'name': 'Analog 5', 'class': 'other' },
}

Object.assign(usages[0], common_target_usages);
Object.assign(usages[2], common_target_usages);
Object.assign(usages[3], common_target_usages);
Object.assign(usages[4], common_target_usages);
Object.assign(usages[5], common_target_usages);
usages[1] = usages[0]; // absolute mouse & keyboard is the same as regular mouse & keyboard

export default usages;
