jfedor2/hid-remapper/config-tool-web/code.js

import crc32 from './crc.js';
import usages from './usages.js';
import examples from './examples.js';

const REPORT_ID_CONFIG = 100;
const REPORT_ID_MONITOR = 101;
const STICKY_FLAG = 1 << 0;
const TAP_FLAG = 1 << 1;
const HOLD_FLAG = 1 << 2;
const CONFIG_SIZE = 32;
const CONFIG_VERSION = 18;
const VENDOR_ID = 0xCAFE;
const PRODUCT_ID = 0xBAF2;
const DEFAULT_PARTIAL_SCROLL_TIMEOUT = 1000000;
const DEFAULT_TAP_HOLD_THRESHOLD = 200000;
const DEFAULT_GPIO_DEBOUNCE_TIME = 5;
const DEFAULT_SCALING = 1000;
const DEFAULT_MACRO_ENTRY_DURATION = 1;

const NLAYERS = 8;
const NMACROS = 32;
const NEXPRESSIONS = 8;
const MACRO_ITEMS_IN_PACKET = 6;
const IGNORE_AUTH_DEV_INPUTS_FLAG = 1 << 4;
const GPIO_OUTPUT_MODE_FLAG = 1 << 5;
const NORMALIZE_GAMEPAD_INPUTS_FLAG = 1 << 6;
const HUB_PORT_NONE = 255;

const QUIRK_FLAG_RELATIVE_MASK = 0b10000000;
const QUIRK_FLAG_SIGNED_MASK = 0b01000000;
const QUIRK_SIZE_MASK = 0b00111111;

const LAYERS_USAGE_PAGE = 0xFFF10000;
const EXPR_USAGE_PAGE = 0xFFF30000;
const MIDI_USAGE_PAGE = 0xFFF70000;
const BUTTON_USAGE_PAGE = 0x00090000;

const RESET_INTO_BOOTSEL = 1;
const SET_CONFIG = 2;
const GET_CONFIG = 3;
const CLEAR_MAPPING = 4;
const ADD_MAPPING = 5;
const GET_MAPPING = 6;
const PERSIST_CONFIG = 7;
const GET_OUR_USAGES = 8;
const GET_THEIR_USAGES = 9;
const SUSPEND = 10;
const RESUME = 11;
const PAIR_NEW_DEVICE = 12;
const CLEAR_BONDS = 13;
const FLASH_B_SIDE = 14;
const CLEAR_MACROS = 15;
const APPEND_TO_MACRO = 16;
const GET_MACRO = 17;
const INVALID_COMMAND = 18;
const CLEAR_EXPRESSIONS = 19;
const APPEND_TO_EXPRESSION = 20;
const GET_EXPRESSION = 21;
const SET_MONITOR_ENABLED = 22;
const CLEAR_QUIRKS = 23;
const ADD_QUIRK = 24;
const GET_QUIRK = 25;

const PERSIST_CONFIG_SUCCESS = 1;
const PERSIST_CONFIG_CONFIG_TOO_BIG = 2;

const ops = {
    "PUSH": 0,
    "PUSH_USAGE": 1,
    "INPUT_STATE": 2,
    "ADD": 3,
    "MUL": 4,
    "EQ": 5,
    "TIME": 6,
    "MOD": 7,
    "GT": 8,
    "NOT": 9,
    "INPUT_STATE_BINARY": 10,
    "ABS": 11,
    "DUP": 12,
    "SIN": 13,
    "COS": 14,
    "DEBUG": 15,
    "AUTO_REPEAT": 16,
    "RELU": 17,
    "CLAMP": 18,
    "SCALING": 19,
    "LAYER_STATE": 20,
    "STICKY_STATE": 21,
    "TAP_STATE": 22,
    "HOLD_STATE": 23,
    "BITWISE_OR": 24,
    "BITWISE_AND": 25,
    "BITWISE_NOT": 26,
    "PREV_INPUT_STATE": 27,
    "PREV_INPUT_STATE_BINARY": 28,
    "STORE": 29,
    "RECALL": 30,
    "SQRT": 31,
    "ATAN2": 32,
    "ROUND": 33,
    "PORT": 34,
    "DPAD": 35,
    "EOL": 36,
    "INPUT_STATE_FP32": 37,
    "PREV_INPUT_STATE_FP32": 38,
    "MIN": 39,
    "MAX": 40,
    "IFTE": 41,
    "DIV": 42,
    "SWAP": 43,
    "MONITOR": 44,
    "SIGN": 45,
    "SUB": 46,
    "PRINT_IF": 47,
    "TIME_SEC": 48,
    "LT": 49,
    "PLUGGED_IN": 50,
    "INPUT_STATE_SCALED": 51,
    "PREV_INPUT_STATE_SCALED": 52,
    "DEADZONE": 53,
    "DEADZONE2": 54,
};

const opcodes = Object.fromEntries(Object.entries(ops).map(([key, value]) => [value, key]));

const expr_re = /((?:\/\*.*?\*\/)?)((?:(?!\/\*).)*)/gs;

const UINT8 = Symbol('uint8');
const UINT16 = Symbol('uint16');
const UINT32 = Symbol('uint32');
const INT32 = Symbol('int32');

let device = null;
let source_modal = null;
let target_modal = null;
let extra_usages = { 'source': [], 'target': [] };
let config = {
    'version': CONFIG_VERSION,
    'unmapped_passthrough_layers': [0, 1, 2, 3, 4, 5, 6, 7],
    'partial_scroll_timeout': DEFAULT_PARTIAL_SCROLL_TIMEOUT,
    'tap_hold_threshold': DEFAULT_TAP_HOLD_THRESHOLD,
    'gpio_debounce_time_ms': DEFAULT_GPIO_DEBOUNCE_TIME,
    'interval_override': 0,
    'our_descriptor_number': 0,
    'ignore_auth_dev_inputs': false,
    'macro_entry_duration': DEFAULT_MACRO_ENTRY_DURATION,
    'gpio_output_mode': 0,
    'input_labels': 0,
    'normalize_gamepad_inputs': true,
    mappings: [{
        'source_usage': '0x00000000',
        'target_usage': '0x00000000',
        'layers': [0],
        'sticky': false,
        'tap': false,
        'hold': false,
        'scaling': DEFAULT_SCALING,
        'source_port': 0,
        'target_port': 0,
    }],
    macros: [
        [], [], [], [], [], [], [], [], [], [], [], [], [], [], [], [],
        [], [], [], [], [], [], [], [], [], [], [], [], [], [], [], []
    ],
    expressions: [
        '', '', '', '', '', '', '', ''
    ],
    quirks: [],
};
let monitor_enabled = false;
let monitor_min_val = {};
let monitor_max_val = {};
let unique_id_counter = 0;
let save_to_device_checkmark_timeout_id = null;
let busy = false;
const ignored_usages = new Set([
]);
let modal_return_mapping = null;
let modal_return_element = null;

document.addEventListener("DOMContentLoaded", function () {
    document.getElementById("open_device").addEventListener("click", open_device);
    document.getElementById("load_from_device").addEventListener("click", load_from_device);
    document.getElementById("save_to_device").addEventListener("click", save_to_device);
    document.getElementById("add_mapping").addEventListener("click", add_mapping_onclick);
    document.getElementById("download_json").addEventListener("click", download_json);
    document.getElementById("upload_json").addEventListener("click", upload_json);
    document.getElementById("flash_firmware").addEventListener("click", flash_firmware);
    document.getElementById("flash_b_side").addEventListener("click", flash_b_side);
    document.getElementById("pair_new_device").addEventListener("click", pair_new_device);
    document.getElementById("clear_bonds").addEventListener("click", clear_bonds);
    document.getElementById("monitor_clear").addEventListener("click", monitor_clear);
    document.getElementById("file_input").addEventListener("change", file_uploaded);
    document.getElementById("add_quirk").addEventListener("click", add_empty_quirk);

    device_buttons_set_disabled_state(true);

    document.getElementById("partial_scroll_timeout_input").addEventListener("change", partial_scroll_timeout_onchange);
    document.getElementById("tap_hold_threshold_input").addEventListener("change", tap_hold_threshold_onchange);
    document.getElementById("gpio_debounce_time_input").addEventListener("change", gpio_debounce_time_onchange);
    document.getElementById("macro_entry_duration_input").addEventListener("change", macro_entry_duration_onchange);
    for (let i = 0; i < NLAYERS; i++) {
        document.getElementById("unmapped_passthrough_checkbox" + i).addEventListener("change", unmapped_passthrough_onchange);
    }
    document.getElementById("interval_override_dropdown").addEventListener("change", interval_override_onchange);
    document.getElementById("our_descriptor_number_dropdown").addEventListener("change", our_descriptor_number_onchange);
    document.getElementById("gpio_output_mode_dropdown").addEventListener("change", gpio_output_mode_onchange);
    document.getElementById("input_labels_dropdown").addEventListener("change", input_labels_onchange("input_labels_dropdown"));
    document.getElementById("input_labels_modal_dropdown").addEventListener("change", input_labels_onchange("input_labels_modal_dropdown"));
    document.getElementById("ignore_auth_dev_inputs_checkbox").addEventListener("change", ignore_auth_dev_inputs_onchange);
    document.getElementById("normalize_gamepad_inputs_checkbox").addEventListener("change", normalize_gamepad_inputs_onchange);

    document.getElementById("nav-monitor-tab").addEventListener("shown.bs.tab", monitor_tab_shown);
    document.getElementById("nav-monitor-tab").addEventListener("hide.bs.tab", monitor_tab_hide);

    document.getElementById("input-column-header").addEventListener("click", sort_by(['source_port', 'source_usage', 'target_usage', 'layers']));
    document.getElementById("output-column-header").addEventListener("click", sort_by(['target_usage', 'source_port', 'source_usage', 'layers']));
    document.getElementById("layer-column-header").addEventListener("click", sort_by(['layers', 'source_port', 'source_usage', 'target_usage']));

    if ("hid" in navigator) {
        navigator.hid.addEventListener('disconnect', hid_on_disconnect);
    } else {
        display_error("Your browser doesn't support WebHID. Try Chrome (desktop version) or a Chrome-based browser.");
    }

    setup_examples();
    source_modal = new bootstrap.Modal(document.getElementById('source_usage_modal'), {});
    target_modal = new bootstrap.Modal(document.getElementById('target_usage_modal'), {});
    setup_macros();
    setup_expressions();
    set_ui_state();
});

async function open_device() {
    if (busy) {
        return;
    }
    busy = true;

    clear_error();
    let success = false;

    try {
        const devices = await navigator.hid.requestDevice({
            filters: [{ usagePage: 0xFF00, usage: 0x0020 }]
        });
        const config_interface = devices?.find(d => d.collections.some(c => c.usagePage == 0xff00));
        if (config_interface !== undefined) {
            device = config_interface;
            if (!device.opened) {
                await device.open().catch((err) => { display_error(err + "\nIf you're on Linux, you might need to give yourself permissions to the appropriate /dev/hidraw* device."); });
            }
            success = device.opened;
            success &&= await check_device_version();
            if (success) {
                device.addEventListener('inputreport', input_report_received);
                await set_monitor_enabled(monitor_enabled);
                await get_usages_from_device();
                setup_usages_modals();
                bluetooth_buttons_set_visibility(device.productName.includes("Bluetooth"));
            }
        }
    } catch (e) {
        display_error(e);
    }

    device_buttons_set_disabled_state(!success);

    if (!success) {
        device = null;
    }

    busy = false;
}

async function load_from_device() {
    if (device == null) {
        return;
    }

    if (busy) {
        return;
    }
    busy = true;

    clear_error();

    document.getElementById('load_from_device').disabled = true;

    try {
        await send_feature_command(GET_CONFIG);
        const [config_version, flags, unmapped_passthrough_layer_mask, partial_scroll_timeout, mapping_count, our_usage_count, their_usage_count, interval_override, tap_hold_threshold, gpio_debounce_time_ms, our_descriptor_number, macro_entry_duration, quirk_count] =
            await read_config_feature([UINT8, UINT8, UINT8, UINT32, UINT16, UINT32, UINT32, UINT8, UINT32, UINT8, UINT8, UINT8, UINT16]);
        check_received_version(config_version);

        config['version'] = config_version;
        config['unmapped_passthrough_layers'] = mask_to_layer_list(unmapped_passthrough_layer_mask);
        config['partial_scroll_timeout'] = partial_scroll_timeout;
        config['tap_hold_threshold'] = tap_hold_threshold;
        config['gpio_debounce_time_ms'] = gpio_debounce_time_ms;
        config['interval_override'] = interval_override;
        config['our_descriptor_number'] = our_descriptor_number;
        config['ignore_auth_dev_inputs'] = !!(flags & IGNORE_AUTH_DEV_INPUTS_FLAG);
        config['gpio_output_mode'] = (flags & GPIO_OUTPUT_MODE_FLAG) ? 1 : 0;
        config['normalize_gamepad_inputs'] = !!(flags & NORMALIZE_GAMEPAD_INPUTS_FLAG);
        config['macro_entry_duration'] = macro_entry_duration + 1;
        config['mappings'] = [];

        for (let i = 0; i < mapping_count; i++) {
            await send_feature_command(GET_MAPPING, [[UINT32, i]]);
            const [target_usage, source_usage, scaling, layer_mask, mapping_flags, hub_ports] =
                await read_config_feature([UINT32, UINT32, INT32, UINT8, UINT8, UINT8]);
            config['mappings'].push({
                'target_usage': '0x' + target_usage.toString(16).padStart(8, '0'),
                'source_usage': '0x' + source_usage.toString(16).padStart(8, '0'),
                'scaling': scaling,
                'layers': mask_to_layer_list(layer_mask),
                'sticky': (mapping_flags & STICKY_FLAG) != 0,
                'tap': (mapping_flags & TAP_FLAG) != 0,
                'hold': (mapping_flags & HOLD_FLAG) != 0,
                'source_port': hub_ports & 0x0F,
                'target_port': (hub_ports >> 4) & 0x0F,
            });
        }

        config['macros'] = [];

        for (let macro_i = 0; macro_i < NMACROS; macro_i++) {
            let macro = [];
            let i = 0;
            let keep_going = true;
            while (keep_going) {
                await send_feature_command(GET_MACRO, [[UINT32, macro_i], [UINT32, i]]);
                const fields = await read_config_feature([UINT8, UINT32, UINT32, UINT32, UINT32, UINT32, UINT32]);
                const nitems = fields[0];
                const usages_ = fields.slice(1);
                if (nitems < MACRO_ITEMS_IN_PACKET) {
                    keep_going = false;
                }
                if ((macro.length == 0) && (nitems > 0)) {
                    macro = [[]];
                }
                for (const usage of usages_.slice(0, nitems)) {
                    if (usage == 0) {
                        macro.push([]);
                    } else {
                        macro.at(-1).push('0x' + usage.toString(16).padStart(8, '0'));
                    }
                }
                i += MACRO_ITEMS_IN_PACKET;
            }

            config['macros'].push(macro);
        }

        config['expressions'] = [];

        for (let expr_i = 0; expr_i < NEXPRESSIONS; expr_i++) {
            let expression = [];
            let i = 0;
            while (true) {
                await send_feature_command(GET_EXPRESSION, [[UINT32, expr_i], [UINT32, i]]);
                const fields = await read_config_feature([UINT8, UINT8, UINT8, UINT8, UINT8, UINT8, UINT8, UINT8, UINT8, UINT8, UINT8, UINT8, UINT8, UINT8, UINT8, UINT8, UINT8, UINT8, UINT8, UINT8, UINT8, UINT8, UINT8, UINT8, UINT8, UINT8, UINT8, UINT8]);
                const nelems = fields[0];
                if (nelems == 0) {
                    break;
                }
                let elems = fields.slice(1);
                for (let j = 0; j < nelems; j++) {
                    const elem = elems[0];
                    elems = elems.slice(1);
                    if ([ops['PUSH'], ops['PUSH_USAGE']].includes(elem)) {
                        const val = elems[3] << 24 | elems[2] << 16 | elems[1] << 8 | elems[0];
                        elems = elems.slice(4);
                        if (elem == ops['PUSH']) {
                            expression.push(val.toString());
                        } else {
                            expression.push('0x' + (val >>> 0).toString(16).padStart(8, '0'));
                        }
                    } else {
                        expression.push(opcodes[elem].toLowerCase());
                    }
                }
                i += nelems;
            }

            config['expressions'].push(expression.join(' '));
        }

        config['quirks'] = [];

        for (let quirk_i = 0; quirk_i < quirk_count; quirk_i++) {
            await send_feature_command(GET_QUIRK, [[UINT32, quirk_i]]);
            const [vendor_id, product_id, interface_, report_id, usage, bitpos, size_flags] =
                await read_config_feature([UINT16, UINT16, UINT8, UINT8, UINT32, UINT16, UINT8]);
            config['quirks'].push({
                'vendor_id': '0x' + vendor_id.toString(16).padStart(4, '0'),
                'product_id': '0x' + product_id.toString(16).padStart(4, '0'),
                'interface': interface_,
                'report_id': report_id,
                'usage': '0x' + usage.toString(16).padStart(8, '0'),
                'bitpos': bitpos,
                'size': size_flags & QUIRK_SIZE_MASK,
                'relative': (size_flags & QUIRK_FLAG_RELATIVE_MASK) != 0,
                'signed': (size_flags & QUIRK_FLAG_SIGNED_MASK) != 0,
            });
        }

        set_ui_state();
        validate_ui_expressions();
    } catch (e) {
        display_error(e);
    }

    if (device != null) {
        document.getElementById('load_from_device').disabled = false;
    }

    busy = false;
}
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
